MOSH-Insa-Toulouse/2024-2025-4GP-Maelys-chr-Buhahahhahah/3d-models/1.png

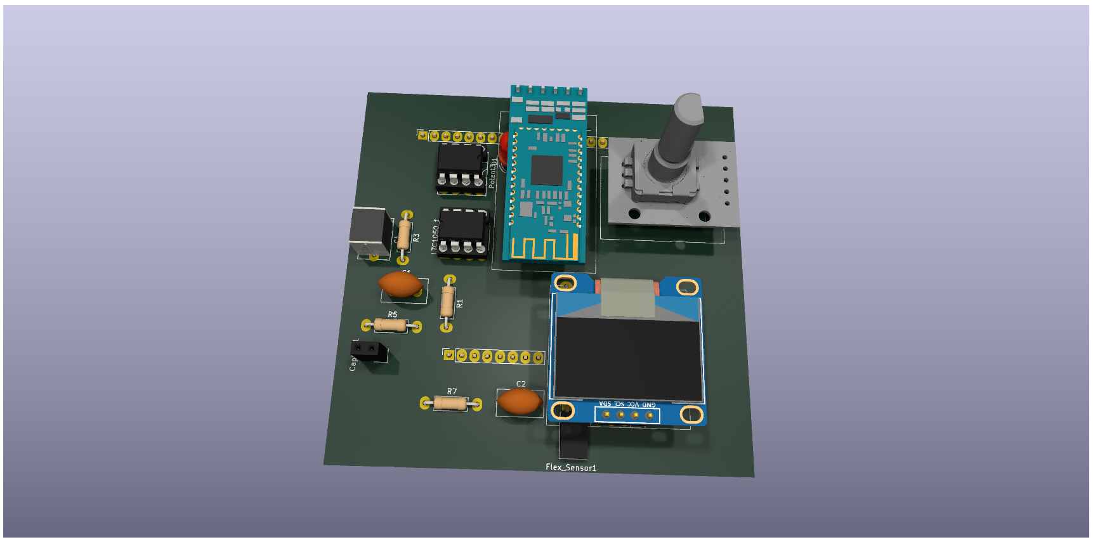
3d-models/1.png
