MOSH-Insa-Toulouse/2024-2025-4GP-Maelys-chr-Buhahahhahah/ltspice/ampli transimpedance capteur publi.asc

C1: cap; 100n
C2: cap; 100n
C3: cap; 100n
C4: cap; 1µ
C5: cap; 1p
R1: res; 100k
R2: res; 1k
R3: res; 100k
R5: res; 10k
R6: res; 1k
U1: LTC1050
V1: voltage; 5V
V2: voltage; PULSE(0 1 0.2 0.1 0.1 3)
V3: voltage; SINE(0 325 50)
X1: capteur_graphite
Named nets: 0, ADC
.tran 5
