MOSH-Insa-Toulouse/2024-2025-4GP-Maelys-chr-Buhahahhahah/ltspice/ampli transimpedance.asc

C1: cap; 100n
C2: cap; 100n
C3: cap; 100n
C4: cap; 1µ
I1: current; PULSE(50n 100n 1 0.1 0.1 2); AC 1 0
R1: res; 100k
R2: res; 1k
R3: res; 100k
R5: res; 10k
R6: res; 1k
U1: LTC1050
V1: voltage; 5V
Named nets: 0, ADC
;tran 4
.ac dec 100 1 1G
